kliuengineering/SmartValve/FRDMK66/bmp3/bmp3.h

/**
* Copyright (c) 2022 Bosch Sensortec GmbH. All rights reserved.
*
* BSD-3-Clause
*
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
* 1. Redistributions of source code must retain the above copyright
*    notice, this list of conditions and the following disclaimer.
*
* 2. Redistributions in binary form must reproduce the above copyright
*    notice, this list of conditions and the following disclaimer in the
*    documentation and/or other materials provided with the distribution.
*
* 3. Neither the name of the copyright holder nor the names of its
*    contributors may be used to endorse or promote products derived from
*    this software without specific prior written permission.
*
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
* @file       bmp3.h
* @date       2022-04-01
* @version    v2.0.6
*
*/

/*!
 * @defgroup bmp3 BMP3
 */

 #ifndef _BMP3_H
 #define _BMP3_H
 
 /* Header includes */
 #include "bmp3_defs.h"
 
 /*! CPP guard */
 #ifdef __cplusplus
 extern "C" {
 #endif
 
 /**
  * \ingroup bmp3
  * \defgroup bmp3ApiInit Initialization
  * @brief Initialize the sensor and device structure
  */
 
 /*!
  * \ingroup bmp3ApiInit
  * \page bmp3_api_bmp3_init bmp3_init
  * \code
  * int8_t bmp3_init(struct bmp3_dev *dev);
  * \endcode
  * @details This API is the entry point.
  * Performs the selection of I2C/SPI read mechanism according to the
  * selected interface and reads the chip-id and calibration data of the sensor.
  *
  *  @param[in,out] dev : Structure instance of bmp3_dev
  *
  * @return Result of API execution status
  * @retval 0  -> Success
  * @retval >0 -> Warning
  * @retval <0 -> Error
  */
 int8_t bmp3_init(struct bmp3_dev *dev);
 
 /**
  * \ingroup bmp3
  * \defgroup bmp3ApiSoftReset Soft reset
  * @brief Perform soft reset of the sensor
  */
 
 /*!
  * \ingroup bmp3ApiSoftReset
  * \page bmp3_api_bmp3_soft_reset bmp3_soft_reset
  * \code
  * int8_t bmp3_soft_reset(const struct bmp3_dev *dev);
  * \endcode
  * @details This API performs the soft reset of the sensor.
  *
  * @param[in] dev : Structure instance of bmp3_dev.
  *
  * @return Result of API execution status
  * @retval 0  -> Success
  * @retval >0 -> Warning
  * @retval <0 -> Error
  */
 int8_t bmp3_soft_reset(struct bmp3_dev *dev);
 
 /**
  * \ingroup bmp3
  * \defgroup bmp3ApiSensorS Sensor settings
  * @brief Get / Set sensor settings
  */
 
 /*!
  * \ingroup bmp3ApiSensorS
  * \page bmp3_api_bmp3_set_sensor_settings bmp3_set_sensor_settings
  * \code
  * int8_t bmp3_set_sensor_settings(uint32_t desired_settings, struct bmp3_settings *settings, struct bmp3_dev *dev);
  * \endcode
  * @details This API sets the power control(pressure enable and
  * temperature enable), over sampling, odr and filter
  * settings in the sensor.
  *
  * @param[in] desired_settings : Variable used to select the settings which
  *                               are to be set in the sensor.
  * @param[in] settings         : Structure instance of bmp3_settings
  * @param[in] dev              : Structure instance of bmp3_dev.
  *
  * @note : Below are the macros to be used by the user for selecting the
  * desired settings. User can do OR operation of these macros for configuring
  * multiple settings.
  *
  *@verbatim
  * ---------------------|----------------------------------------------
  * desired_settings     |   Functionality
  * ---------------------|----------------------------------------------
  * BMP3_SEL_PRESS_EN    |   Enable/Disable pressure.
  * BMP3_SEL_TEMP_EN     |   Enable/Disable temperature.
  * BMP3_SEL_PRESS_OS    |   Set pressure oversampling.
  * BMP3_SEL_TEMP_OS     |   Set temperature oversampling.
  * BMP3_SEL_IIR_FILTER  |   Set IIR filter.
  * BMP3_SEL_ODR         |   Set ODR.
  * BMP3_SEL_OUTPUT_MODE |   Set either open drain or push pull
  * BMP3_SEL_LEVEL       |   Set interrupt pad to be active high or low
  * BMP3_SEL_LATCH       |   Set interrupt pad to be latched or nonlatched.
  * BMP3_SEL_DRDY_EN     |   Map/Unmap the drdy interrupt to interrupt pad.
  * BMP3_SEL_I2C_WDT_EN  |   Enable/Disable I2C internal watch dog.
  * BMP3_SEL_I2C_WDT     |   Set I2C watch dog timeout delay.
  * ---------------------|----------------------------------------------
  *@endverbatim
  *
  * @return Result of API execution status
  * @retval 0  -> Success
  * @retval >0 -> Warning
  * @retval <0 -> Error
  */
 int8_t bmp3_set_sensor_settings(uint32_t desired_settings, struct bmp3_settings *settings, struct bmp3_dev *dev);
 
 /*!
  * \ingroup bmp3ApiSensorS
  * \page bmp3_api_bmp3_get_sensor_settings bmp3_get_sensor_settings
  * \code
  * int8_t bmp3_get_sensor_settings(struct bmp3_settings *settings, struct bmp3_dev *dev);
  * \endcode
  * @details This API gets the power control(power mode, pressure enable and
  * temperature enable), over sampling, odr, filter, interrupt control and
  * advance settings from the sensor.
  *
  * @param[out] settings       : Structure instance of bmp3_settings
  * @param[in] dev             : Structure instance of bmp3_dev.
  *
  * @return Result of API execution status
  * @retval 0  -> Success
  * @retval >0 -> Warning
  * @retval <0 -> Error
  */
 int8_t bmp3_get_sensor_settings(struct bmp3_settings *settings, struct bmp3_dev *dev);
 
 /**
  * \ingroup bmp3
  * \defgroup bmp3ApiPowermode Power mode
  * @brief Set / Get power mode of the sensor
  */
 
 /*!
  * \ingroup bmp3ApiPowermode
  * \page bmp3_api_bmp3_set_op_mode bmp3_set_op_mode
  * \code
  * int8_t bmp3_set_op_mode(struct bmp3_settings *settings, struct bmp3_dev *dev);
  * \endcode
  * @details This API sets the power mode of the sensor.
  *
  * @param[in] settings       : Structure instance of bmp3_settings
  * @param[in] dev            : Structure instance of bmp3_dev.
  *
  *@verbatim
  * ----------------------|-------------------
  * dev->settings.op_mode |   Macros
  * ----------------------|-------------------
  *     0                 | BMP3_MODE_SLEEP
  *     1                 | BMP3_MODE_FORCED
  *     3                 | BMP3_MODE_NORMAL
  * ----------------------|-------------------
  *@endverbatim
  *
  * @note : Before setting normal mode, valid odr and osr settings should be set
  * in the sensor by using 'bmp3_set_sensor_settings' function.
  *
  * @return Result of API execution status
  * @retval 0  -> Success
  * @retval >0 -> Warning
  * @retval <0 -> Error
  */
 int8_t bmp3_set_op_mode(struct bmp3_settings *settings, struct bmp3_dev *dev);
 
 /*!
  * \ingroup bmp3ApiPowermode
  * \page bmp3_api_bmp3_get_op_mode bmp3_get_op_mode
  * \code
  * int8_t bmp3_get_op_mode(uint8_t *op_mode, const struct bmp3_dev *dev);
  * \endcode
  * @details This API gets the power mode of the sensor.
  *
  * @param[in] dev      : Structure instance of bmp3_dev.
  * @param[out] op_mode : Pointer variable to store the op-mode.
  *
  *@verbatim
  * ------------------------------------------
  *   op_mode             |   Macros
  * ----------------------|-------------------
  *     0                 | BMP3_MODE_SLEEP
  *     1                 | BMP3_MODE_FORCED
  *     3                 | BMP3_MODE_NORMAL
  * ------------------------------------------
  *@endverbatim
  *
  * @return Result of API execution status
  * @retval 0  -> Success
  * @retval >0 -> Warning
  * @retval <0 -> Error
  */
 int8_t bmp3_get_op_mode(uint8_t *op_mode, struct bmp3_dev *dev);
 
 /**
  * \ingroup bmp3
  * \defgroup bmp3ApiData Sensor Data
  * @brief Get Sensor data
  */
 
 /*!
  * \ingroup bmp3ApiData
  * \page bmp3_api_bmp3_get_sensor_data bmp3_get_sensor_data
  * \code
  * int8_t bmp3_get_sensor_data(uint8_t sensor_comp, struct bmp3_data *data, struct bmp3_dev *dev);
  * \endcode
  * @details This API reads the pressure, temperature or both data from the
  * sensor, compensates the data and store it in the bmp3_data structure
  * instance passed by the user.
  *
  * @param[in] sensor_comp : Variable which selects which data to be read from
  * the sensor.
  *
  *@verbatim
  * sensor_comp |   Macros
  * ------------|-------------------
  *     1       | BMP3_PRESS
  *     2       | BMP3_TEMP
  *     3       | BMP3_ALL
  *@endverbatim
  *
  * @param[out] data : Structure instance of bmp3_data.
  * @param[in] dev   : Structure instance of bmp3_dev.
  *
  * @note : For fixed point the compensated temperature and pressure has a multiplication factor of 100.
  *         Units are degree celsius and Pascal respectively.
  *         ie. If temperature is 2426 then temperature is 24.26 deg C
  *         If press is 9528709, then pressure is 95287.09 Pascal.
  *
  * @return Result of API execution status
  * @retval 0  -> Success
  * @retval >0 -> Warning
  * @retval <0 -> Error
  */
 int8_t bmp3_get_sensor_data(uint8_t sensor_comp, struct bmp3_data *data, struct bmp3_dev *dev);
 
 /**
  * \ingroup bmp3
  * \defgroup bmp3ApiRegs Registers
  * @brief Read / Write data to the given register address
  */
 
 /*!
  * \ingroup bmp3ApiRegs
  * \page bmp3_api_bmp3_set_regs bmp3_set_regs
  * \code
  * int8_t bmp3_set_regs(uint8_t *reg_addr, const uint8_t *reg_data, uint8_t len, const struct bmp3_dev *dev);
  * \endcode
  * @details This API writes the given data to the register address
  * of the sensor.
  *
  *  @param[in] reg_addr  : Register address to where the data to be written.
  *  @param[in] reg_data  : Pointer to data buffer which is to be written
  *                         in the sensor.
  *  @param[in] len       : No. of bytes of data to write.
  *  @param[in] dev       : Structure instance of bmp3_dev.
  *
  * @return Result of API execution status
  * @retval 0  -> Success
  * @retval >0 -> Warning
  * @retval <0 -> Error
  */
 int8_t bmp3_set_regs(uint8_t *reg_addr, const uint8_t *reg_data, uint32_t len, struct bmp3_dev *dev);
 
 /*!
  * \ingroup bmp3ApiRegs
  * \page bmp3_api_bmp3_get_regs bmp3_get_regs
  * \code
  * int8_t bmp3_get_regs(uint8_t reg_addr, uint8_t *reg_data, uint16_t length, const struct bmp3_dev *dev);
  * \endcode
  * @details This API reads the data from the given register address of the sensor.
  *
  *  @param[in] reg_addr  : Register address from where the data to be read
  *  @param[out] reg_data : Pointer to data buffer to store the read data.
  *  @param[in] len       : No. of bytes of data to be read.
  *  @param[in] dev       : Structure instance of bmp3_dev.
  *
  * @return Result of API execution status
  * @retval 0  -> Success
  * @retval >0 -> Warning
  * @retval <0 -> Error
  */
 int8_t bmp3_get_regs(uint8_t reg_addr, uint8_t *reg_data, uint32_t len, struct bmp3_dev *dev);
 
 /**
  * \ingroup bmp3
  * \defgroup bmp3ApiFIFO FIFO
  * @brief FIFO operations of the sensor
  */
 
 /*!
  * \ingroup bmp3ApiFIFO
  * \page bmp3_api_bmp3_set_fifo_settings bmp3_set_fifo_settings
  * \code
  * int8_t bmp3_set_fifo_settings(uint16_t desired_settings, struct bmp3_fifo_settings *fifo_settings,
  *                             struct bmp3_dev *dev);
  * \endcode
  * @details This API sets the fifo_config_1(fifo_mode,
  * fifo_stop_on_full, fifo_time_en, fifo_press_en, fifo_temp_en),
  * fifo_config_2(fifo_subsampling, data_select) and int_ctrl(fwtm_en, ffull_en)
  * settings in the sensor.
  *
  * @param[in] desired_settings : Variable used to select the FIFO settings which
  *                               are to be set in the sensor.
  *
  * @note : Below are the macros to be used by the user for selecting the
  * desired settings. User can do OR operation of these macros for configuring
  * multiple settings.
  *
  *@verbatim
  * --------------------------------|---------------------------------------------
  *      desired_settings           |  Functionality
  * --------------------------------|---------------------------------------------
  * BMP3_SEL_FIFO_MODE              |  Enable/Disable FIFO
  * BMP3_SEL_FIFO_STOP_ON_FULL_EN   |  Set FIFO stop on full interrupt
  * BMP3_SEL_FIFO_TIME_EN           |  Enable/Disable FIFO time
  * BMP3_SEL_FIFO_PRESS_EN          |  Enable/Disable pressure
  * BMP3_SEL_FIFO_TEMP_EN           |  Enable/Disable temperature
  * BMP3_SEL_FIFO_DOWN_SAMPLING     |  Set FIFO downsampling
  * BMP3_SEL_FIFO_FILTER_EN         |  Enable/Disable FIFO filter
  * BMP3_SEL_FIFO_FWTM_EN           |  Enable/Disable FIFO watermark interrupt
  * BMP3_SEL_FIFO_FFULL_EN          |  Enable/Disable FIFO full interrupt
  * --------------------------------|---------------------------------------------
  *@endverbatim
  *
  * @param[in] fifo_settings : Structure instance of bmp3_fifo_settings
  * @param[in] dev           : Structure instance of bmp3_dev.
  *
  * @return Result of API execution status
  * @retval 0  -> Success
  * @retval >0 -> Warning
  * @retval <0 -> Error
  */
 int8_t bmp3_set_fifo_settings(uint16_t desired_settings,
                               const struct bmp3_fifo_settings *fifo_settings,
                               struct bmp3_dev *dev);
 
 /*!
  * \ingroup bmp3ApiFIFO
  * \page bmp3_api_bmp3_get_fifo_settings bmp3_get_fifo_settings
  * \code
  * int8_t bmp3_get_fifo_settings(struct bmp3_fifo_settings *fifo_settings, struct bmp3_dev *dev);
  * \endcode
  * @details This API gets the fifo_config_1(fifo_mode,
  * fifo_stop_on_full, fifo_time_en, fifo_press_en, fifo_temp_en),
  * fifo_config_2(fifo_subsampling, data_select) and int_ctrl(fwtm_en, ffull_en)
  * settings from the sensor.
  *
  * @param[in] fifo_settings : Structure instance of bmp3_fifo_settings
  * @param[in] dev           : Structure instance of bmp3_dev.
  *
  * @return Result of API execution status
  * @retval 0  -> Success
  * @retval >0 -> Warning
  * @retval <0 -> Error
  */
 int8_t bmp3_get_fifo_settings(struct bmp3_fifo_settings *fifo_settings, struct bmp3_dev *dev);
 
 /*!
  * \ingroup bmp3ApiFIFO
  * \page bmp3_api_bmp3_get_fifo_data bmp3_get_fifo_data
  * \code
  * int8_t bmp3_get_fifo_data(struct bmp3_fifo_data *fifo,
  *                         const struct bmp3_fifo_settings *fifo_settings,
  *                         struct bmp3_dev *dev);
  * \endcode
  * @details This API gets the fifo data from the sensor.
  *
  * @param[in,out] fifo      : Structure instance of bmp3_fifo_data
  * @param[in] fifo_settings : Structure instance of bmp3_fifo_settings
  * @param[in] dev           : Structure instance of bmp3_dev
  *
  * @return Result of API execution status.
  * @retval 0  -> Success
  * @retval >0 -> Warning
  * @retval <0 -> Error
  */
 int8_t bmp3_get_fifo_data(struct bmp3_fifo_data *fifo,
                           const struct bmp3_fifo_settings *fifo_settings,
                           struct bmp3_dev *dev);
 
 /*!
  * \ingroup bmp3ApiFIFO
  * \page bmp3_api_bmp3_get_fifo_length bmp3_get_fifo_length
  * \code
  * int8_t bmp3_get_fifo_length(uint16_t *fifo_length, struct bmp3_dev *dev);
  * \endcode
  * @details This API gets the fifo length from the sensor.
  *
  * @param[out] fifo_length : Variable used to store the fifo length.
  * @param[in] dev          : Structure instance of bmp3_dev.
  *
  * @return Result of API execution status.
  * @retval 0  -> Success
  * @retval >0 -> Warning
  * @retval <0 -> Error
  */
 int8_t bmp3_get_fifo_length(uint16_t *fifo_length, struct bmp3_dev *dev);
 
 /*!
  * \ingroup bmp3ApiFIFO
  * \page bmp3_api_bmp3_extract_fifo_data bmp3_extract_fifo_data
  * \code
  * int8_t bmp3_extract_fifo_data(struct bmp3_data *data, struct bmp3_fifo_data *fifo, struct bmp3_dev *dev);
  * \endcode
  * @details This API extracts the temperature and/or pressure data from the FIFO
  * data which is already read from the fifo.
  *
  * @param[out] data : Array of bmp3_data structures where the temperature
  *                    and pressure frames will be stored.
  * @param[in] fifo  : Structure instance of bmp3_fifo_data
  * @param[in] dev   : Structure instance of bmp3_dev
  *
  * @return Result of API execution status.
  * @retval 0  -> Success
  * @retval <0 -> Error
  */
 int8_t bmp3_extract_fifo_data(struct bmp3_data *data, struct bmp3_fifo_data *fifo, struct bmp3_dev *dev);
 
 /*!
  * \ingroup bmp3ApiFIFO
  * \page bmp3_api_bmp3_set_fifo_watermark bmp3_set_fifo_watermark
  * \code
  * int8_t bmp3_set_fifo_watermark(const struct bmp3_fifo_data *fifo,
  *                              const struct bmp3_fifo_settings *fifo_settings,
  *                              struct bmp3_dev *dev);
  * \endcode
  * @details This API sets the fifo watermark length according to the frames count
  * set by the user in the device structure. Refer below for usage.
  *
  * @note: fifo.req_frames = 50;
  *
  * @param[in] fifo          : Structure instance of bmp3_fifo_data
  * @param[in] fifo_settings : Structure instance of bmp3_fifo_settings
  * @param[in] dev           : Structure instance of bmp3_dev
  *
  * @return Result of API execution status.
  * @retval 0  -> Success
  * @retval <0 -> Error
  */
 int8_t bmp3_set_fifo_watermark(const struct bmp3_fifo_data *fifo,
                                const struct bmp3_fifo_settings *fifo_settings,
                                struct bmp3_dev *dev);
 
 /*!
  * \ingroup bmp3ApiFIFO
  * \page bmp3_api_bmp3_get_fifo_watermark bmp3_get_fifo_watermark
  * \code
  * int8_t bmp3_get_fifo_watermark(uint16_t *watermark_len, struct bmp3_dev *dev);
  * \endcode
  * @details This API gets the fifo watermark length according to the frames count
  * set by the user in the device structure
  *
  * @param[in] watermark_len : Watermark level value
  * @param[in] dev           : Structure instance of bmp3_dev
  *
  * @return Result of API execution status.
  * @retval 0  -> Success
  * @retval <0 -> Error
  */
 int8_t bmp3_get_fifo_watermark(uint16_t *watermark_len, struct bmp3_dev *dev);
 
 /*!
  * \ingroup bmp3ApiFIFO
  * \page bmp3_api_bmp3_fifo_flush bmp3_fifo_flush
  * \code
  * int8_t bmp3_fifo_flush(const struct bmp3_dev *dev);
  * \endcode
  * @details This API performs fifo flush
  *
  * @param[in] dev : Structure instance of bmp3_dev.
  *
  * @return Result of API execution status
  * @retval 0  -> Success
  * @retval >0 -> Warning
  * @retval <0 -> Error
  */
 int8_t bmp3_fifo_flush(struct bmp3_dev *dev);
 
 /**
  * \ingroup bmp3
  * \defgroup bmp3ApiStatus Sensor Status
  * @brief Read status of the sensor
  */
 
 /*!
  * \ingroup bmp3ApiStatus
  * \page bmp3_api_bmp3_get_status bmp3_get_status
  * \code
  * int8_t bmp3_get_status(struct bmp3_status *status, struct bmp3_dev *dev);
  * \endcode
  * @details This API gets the command ready, data ready for pressure and
  * temperature and interrupt (fifo watermark, fifo full, data ready) and
  * error status from the sensor.
  *
  * @param[out] status : Structure instance of bmp3_status
  * @param[in] dev     : Structure instance of bmp3_dev
  *
  * @return Result of API execution status.
  * @retval 0  -> Success
  * @retval <0 -> Error
  */
 int8_t bmp3_get_status(struct bmp3_status *status, struct bmp3_dev *dev);
 
 #ifdef __cplusplus
 }
 #endif /* End of CPP guard */
 
 #endif /* _BMP3_H */
 
